slahiri/open-cad/stl/stl_bottom_left.scad

include <../cad/protective_storage_box.scad>
lid_angle = 0;
show_tray_in_assembly = false;
box_bottom_left();
