slahiri/open-cad/cad/stl_lid_middle.scad

include <protective_storage_box.scad>
lid_angle = 0;
show_tray_in_assembly = false;
render_assembly = false;
rotate([180, 0, 0]) translate([-mid_start, -width, -lid_h]) box_lid_middle();
