slahiri/open-cad/cad/stl_plate_box.scad

include <protective_storage_box.scad>
lid_angle = 0;
show_tray_in_assembly = false;
render_assembly = false;
// All box bottom parts on one plate
print_plate_box();
