slahiri/open-cad/cad/stl_plate_lid.scad

include <protective_storage_box.scad>
lid_angle = 0;
show_tray_in_assembly = false;
render_assembly = false;
// All lid parts on one plate
print_plate_lid();
