slahiri/open-cad/cad/stl_plate_small.scad

include <protective_storage_box.scad>
lid_angle = 0;
show_tray_in_assembly = false;
render_assembly = false;
// All tray compartments + hardware on one plate
print_plate_small();
