slahiri/open-cad/cad/stl_tray_right.scad

include <protective_storage_box.scad>
lid_angle = 0;
show_tray_in_assembly = false;
render_assembly = false;
tray_right();
