slahiri/open-cad/cad/stl_weave_frame_right.scad

include <protective_storage_box.scad>
lid_angle = 0;
show_tray_in_assembly = false;
render_assembly = false;
lid_weave_frame_right();
