slahiri/open-cad/cad/stl_weave_y_left.scad

include <protective_storage_box.scad>
lid_angle = 0;
show_tray_in_assembly = false;
render_assembly = false;
lid_weave_y_strips_left();
