slahiri/open-cad/cad/view_closed.scad

// ============================================================================
// VIEW: Closed Box — lid shut, tray inside, latches engaged
// ============================================================================
include <protective_storage_box.scad>

lid_angle = 0;
show_tray_in_assembly = true;
tray_lift = 0;
