slahiri/open-cad/cad/view_open.scad

// ============================================================================
// VIEW: Open Box — lid open 120°, tray resting inside
// ============================================================================
include <protective_storage_box.scad>

lid_angle = 120;
show_tray_in_assembly = true;
tray_lift = 0;
