slahiri/open-cad/cad/view_open_tray_out.scad

// ============================================================================
// VIEW: Open Box — lid open 120°, tray lifted out and floating above
// ============================================================================
include <protective_storage_box.scad>

lid_angle = 120;
show_tray_in_assembly = true;
tray_lift = 80;  // Tray floats 80mm above its resting position
